daedalus-labs/filament-dryer/docs/pcb/dryer-schematic.kicad_sch

## KiCad design docs/pcb/dryer-schematic.kicad_sch (2023-04-24)

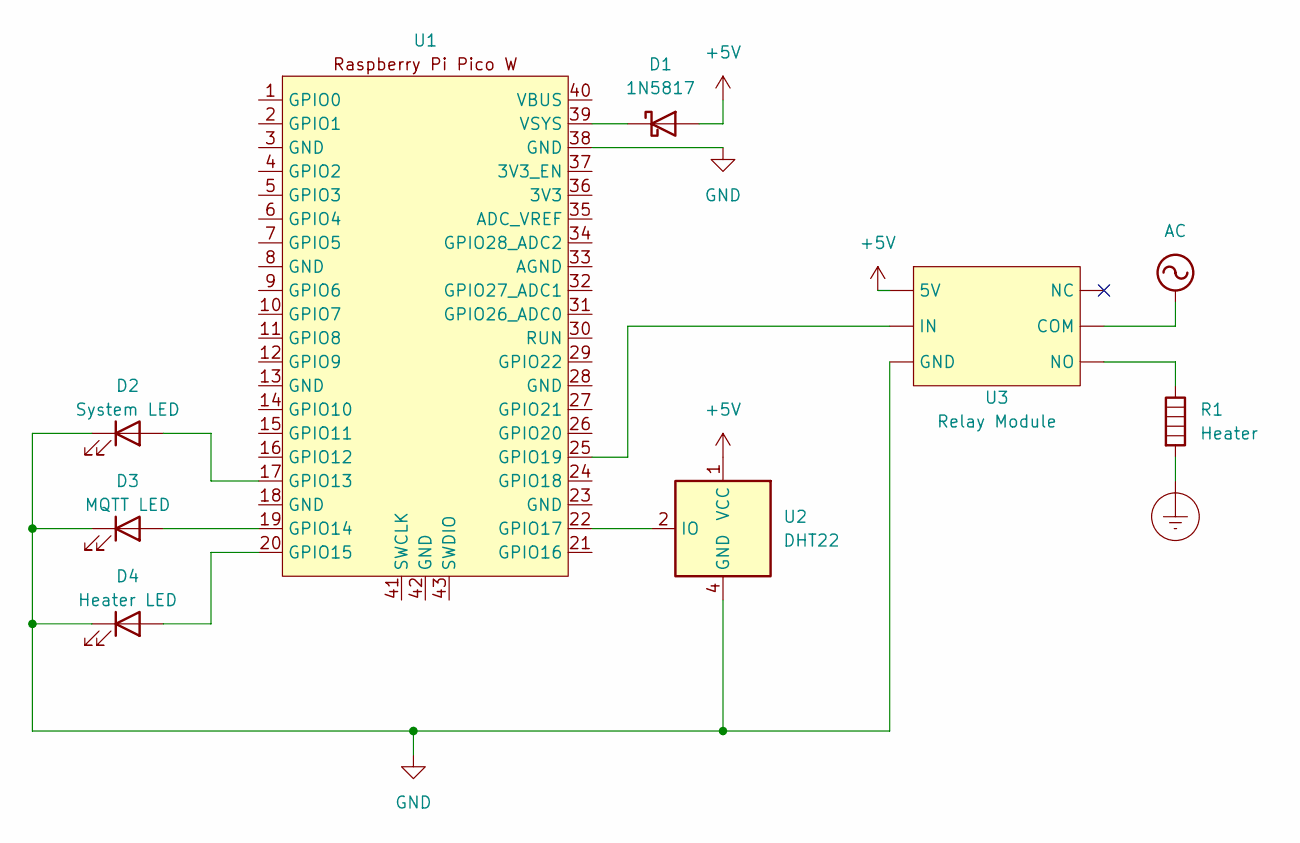
[picture p10: schematic dryer-schematic.kicad_sch]

Parts:
D1: 1N5817; D_DO-41_SOD81_P10.16mm_Horizontal
D2: System LED
D3: MQTT LED
D4: Heater LED
R1: Heater
U1: Pico-W; RPi_Pico_SMD_TH
U2: DHT22; Aosong_DHT11_5.5x12.0_P2.54mm
U3: Relay Module

Connections:
unnamed: D1.1 (K), U1.39 (VSYS)
unnamed: D2.1 (K), D3.1 (K), D4.1 (K), U2.4 (GND), U3.
unnamed: D2.2 (A), U1.17 (GPIO13)
unnamed: D3.2 (A), U1.19 (GPIO14)
unnamed: D4.2 (A), U1.20 (GPIO15)
unnamed: R1.1, U3.
unnamed: U1.22 (GPIO17), U2.2 (IO)
unnamed: U1.25 (GPIO19), U3.
